c0derMo/DIY-HOTAS/Joystick/STLs/Custom Replacements/Button Holders/Secondary_Trigger_Buttonholder [c0].stl

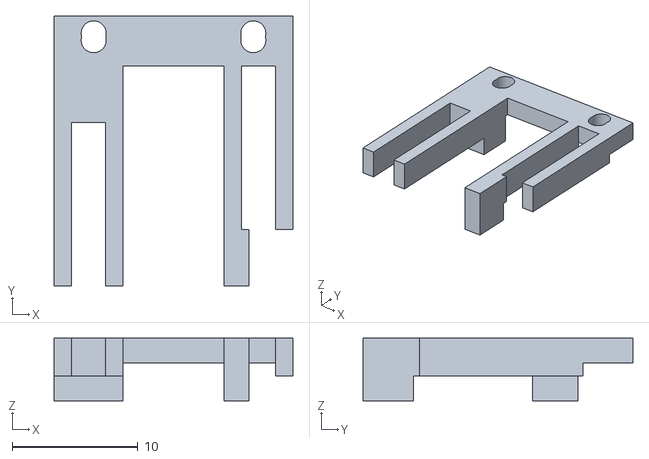
[picture p15: CAD file, 2026-03-30]
Joystick/STLs/Custom Replacements/Button Holders/Secondary_Trigger_Buttonholder [c0].stl
19.0 x 21.5 x 5.00
