c0derMo/DIY-HOTAS/Joystick/STLs/Custom Replacements/Case_Back_With_Mounting_Holes [c0].stl

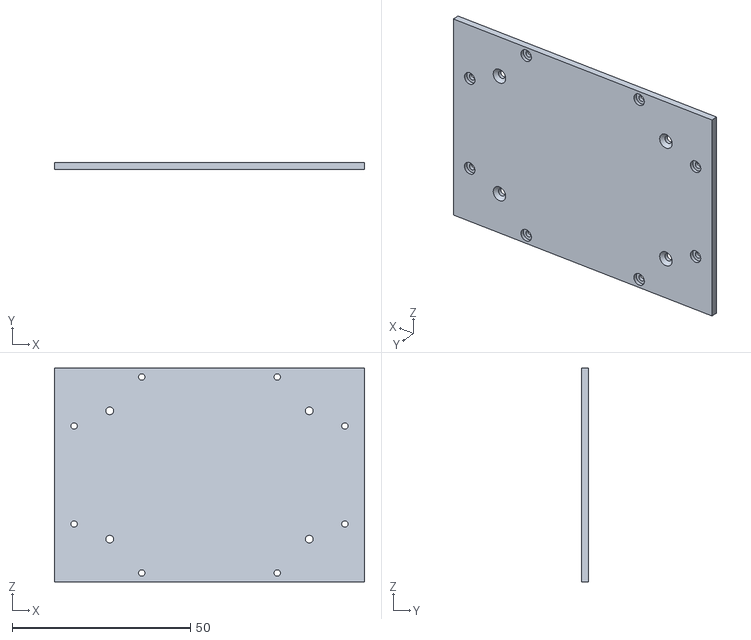
[picture p16: CAD file, 2026-03-30]
Joystick/STLs/Custom Replacements/Case_Back_With_Mounting_Holes [c0].stl
87.0 x 2.00 x 60.0
