c0derMo/DIY-HOTAS/Joystick/STLs/Custom Replacements/Z-Axis/GX12-Bot [c0].stl

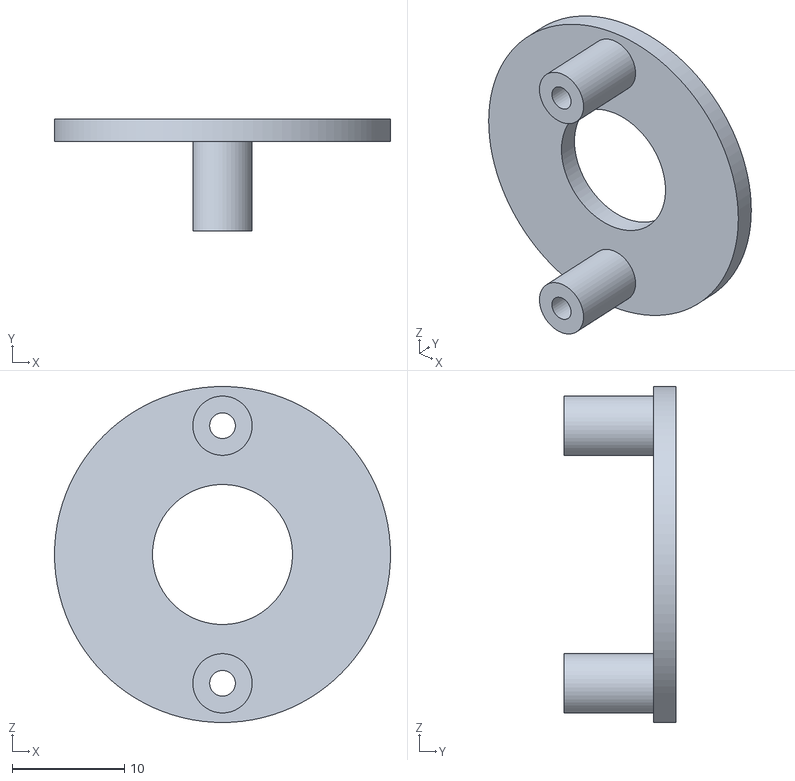
[picture p17: CAD file, 2026-03-30]
Joystick/STLs/Custom Replacements/Z-Axis/GX12-Bot [c0].stl
30.0 x 10.0 x 30.0
