c0derMo/DIY-HOTAS/Joystick/STLs/Gimbal/Gimbal Shaft [B21] [ADD].stl

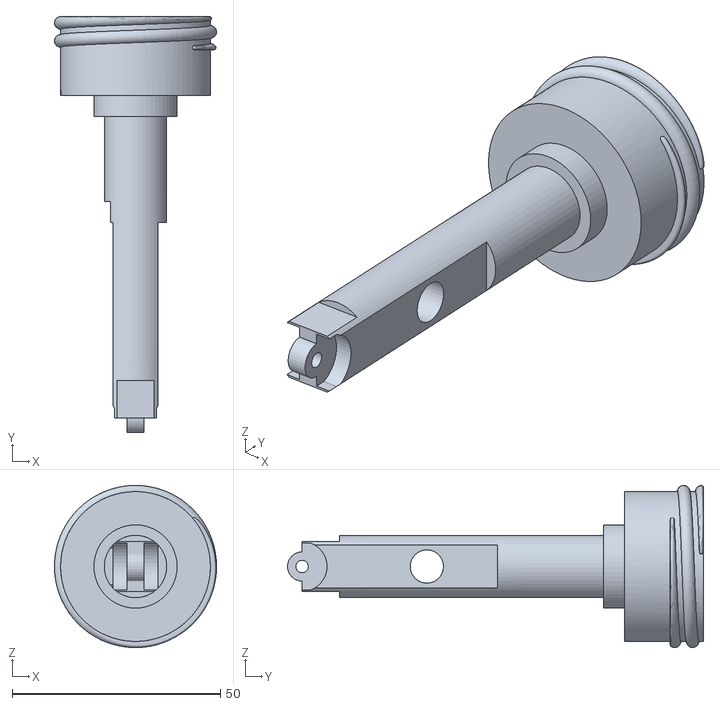
[picture p18: CAD file, 2026-03-30]
Joystick/STLs/Gimbal/Gimbal Shaft [B21] [ADD].stl
39.0 x 100.0 x 39.0
