c0derMo/DIY-HOTAS/Joystick/STLs/Gimbal/GimbalCase/Case Right [B21] [ADD].stl

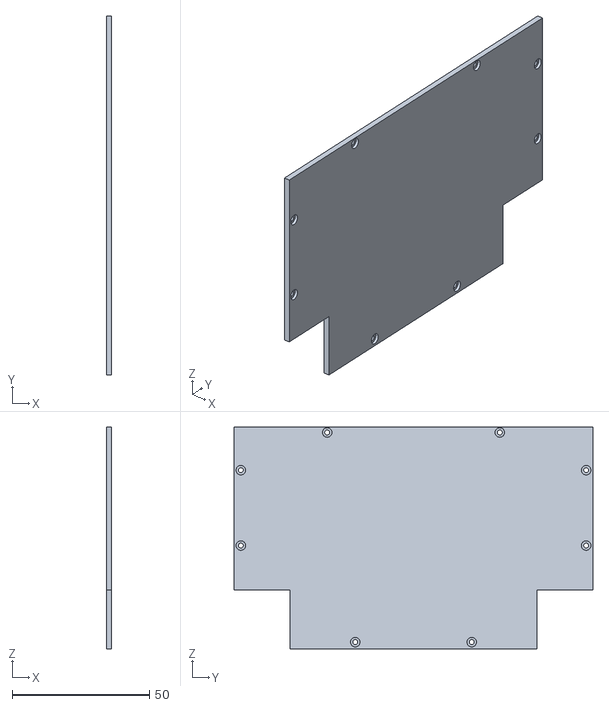
[picture p19: CAD file, 2026-03-30]
Joystick/STLs/Gimbal/GimbalCase/Case Right [B21] [ADD].stl
2.00 x 131.0 x 81.0
