c0derMo/DIY-HOTAS/Joystick/STLs/Head/JoyStick Housing Back [B21].stl

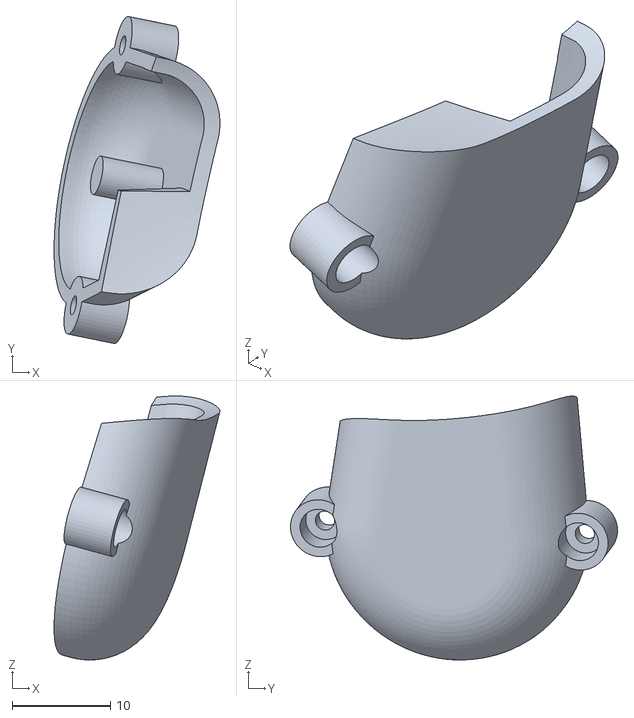
[picture p20: CAD file, 2026-03-30]
Joystick/STLs/Head/JoyStick Housing Back [B21].stl
16.9 x 33.3 x 26.9
