c0derMo/DIY-HOTAS/Joystick/STLs/Head/Tops/Diffuser Top [B21].stl

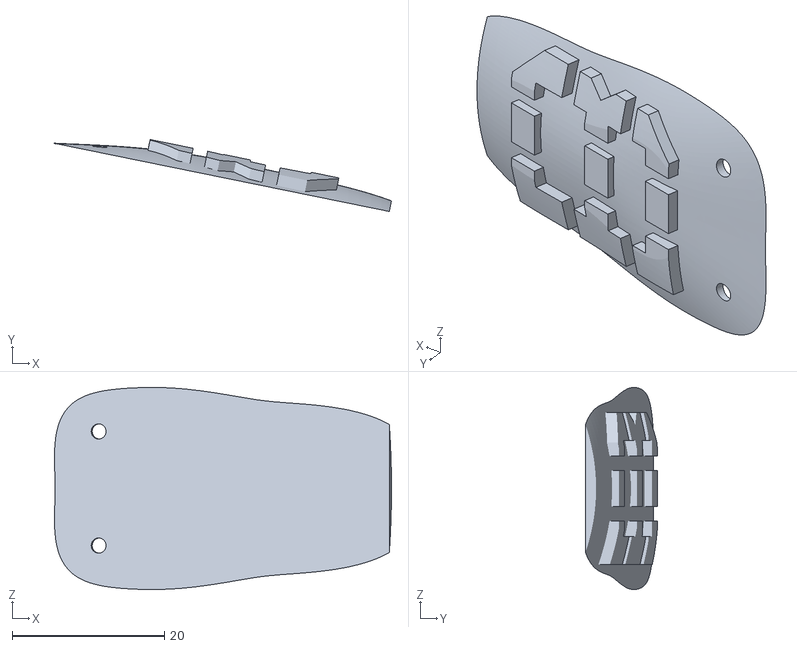
[picture p21: CAD file, 2026-03-30]
Joystick/STLs/Head/Tops/Diffuser Top [B21].stl
44.3 x 9.46 x 26.6
