c0derMo/DIY-HOTAS/Joystick/STLs/Miramaksimus Base Updates/gimbal_frame_as5600.stl

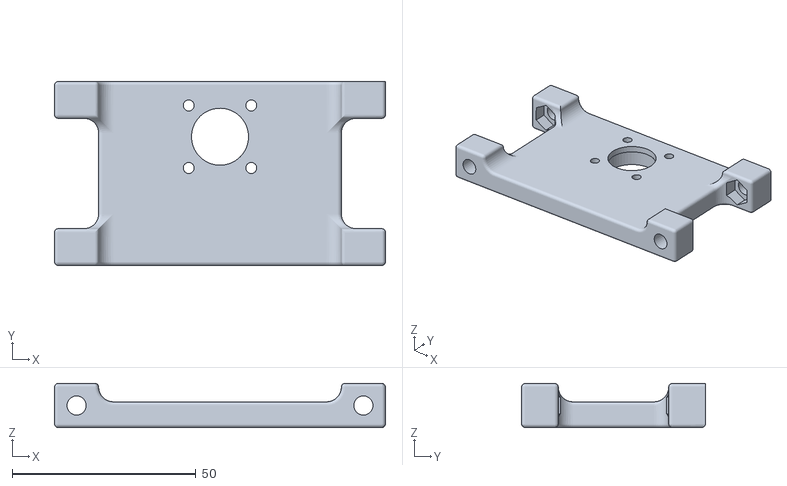
[picture p22: CAD file, 2026-04-03]
Joystick/STLs/Miramaksimus Base Updates/gimbal_frame_as5600.stl
90.0 x 50.0 x 12.0
