c0derMo/DIY-HOTAS/Joystick/STLs/Body/PinkyButton [B21] [ADD].stl

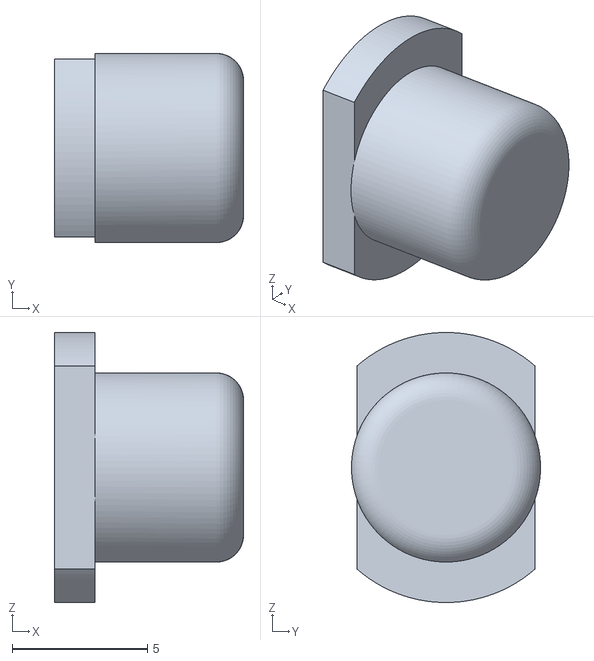
[picture p23: CAD file, 2026-03-30]
Joystick/STLs/Body/PinkyButton [B21] [ADD].stl
7.00 x 7.00 x 10.00
