c0derMo/DIY-HOTAS/Joystick/STLs/Buttons/HS Top 2 [B21].stl

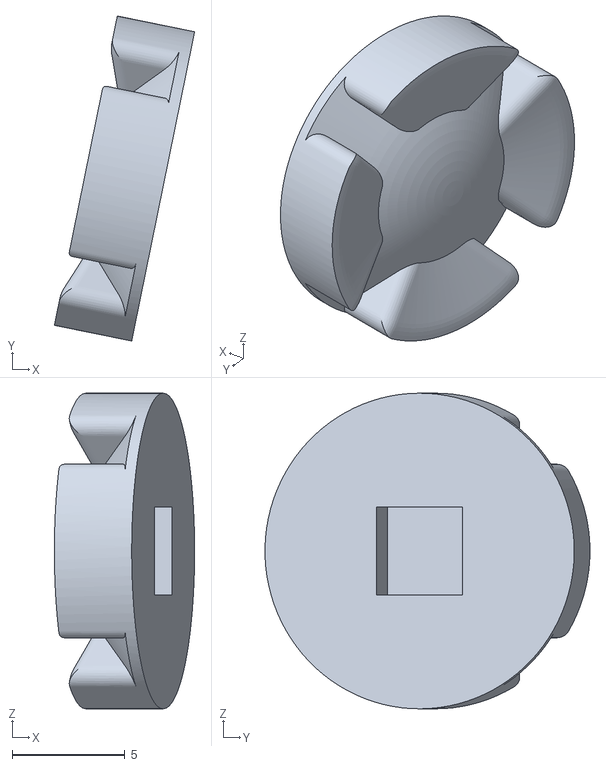
[picture p24: CAD file, 2026-03-30]
Joystick/STLs/Buttons/HS Top 2 [B21].stl
6.22 x 14.4 x 14.0
