c0derMo/DIY-HOTAS/Joystick/STLs/Custom Replacements/Brakelever_Solid [c0].stl

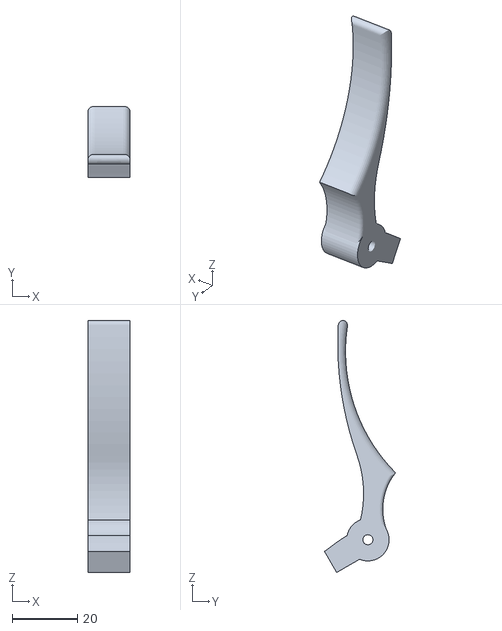
[picture p25: CAD file, 2026-03-30]
Joystick/STLs/Custom Replacements/Brakelever_Solid [c0].stl
13.0 x 21.8 x 77.2
