c0derMo/DIY-HOTAS/Joystick/STLs/Custom Replacements/Button Holders/HAT Thumb Holder [c0].stl

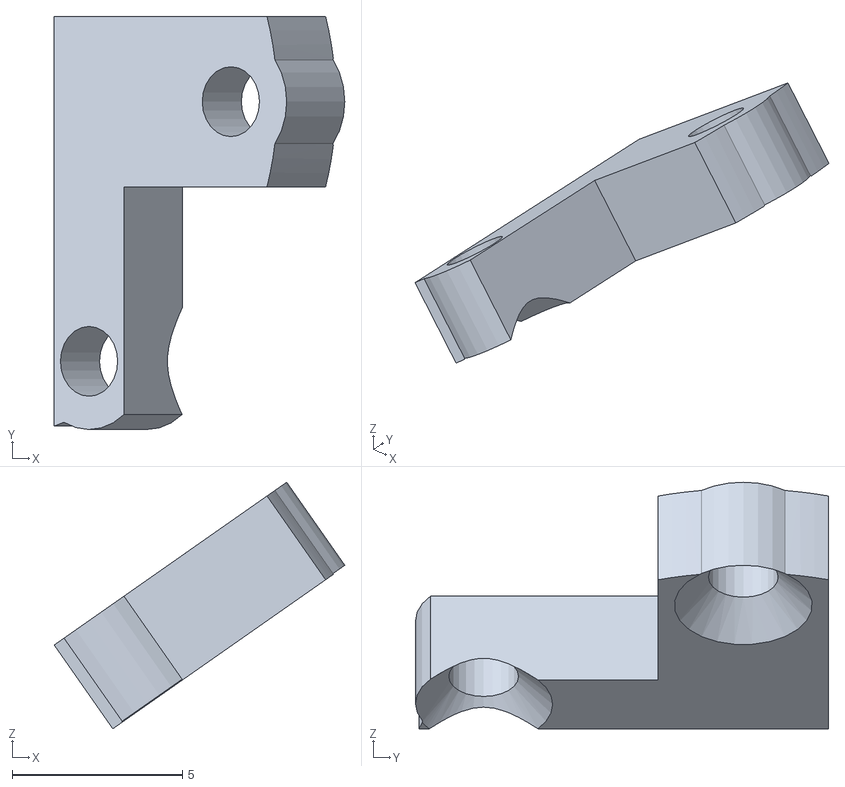
[picture p26: CAD file, 2026-03-30]
Joystick/STLs/Custom Replacements/Button Holders/HAT Thumb Holder [c0].stl
8.53 x 12.1 x 7.24
