c0derMo/DIY-HOTAS/Joystick/STLs/Custom Replacements/Buttons/Button 1 [c0].stl

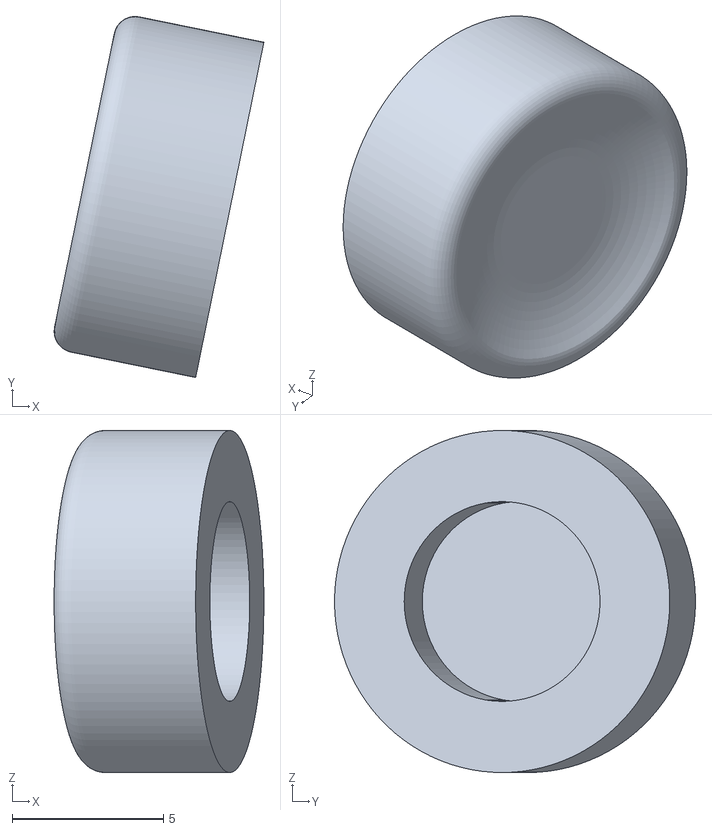
[picture p27: CAD file, 2026-03-30]
Joystick/STLs/Custom Replacements/Buttons/Button 1 [c0].stl
6.93 x 11.9 x 11.3
