c0derMo/DIY-HOTAS/Joystick/STLs/Custom Replacements/Z-Axis/GX12-Top [c0].stl

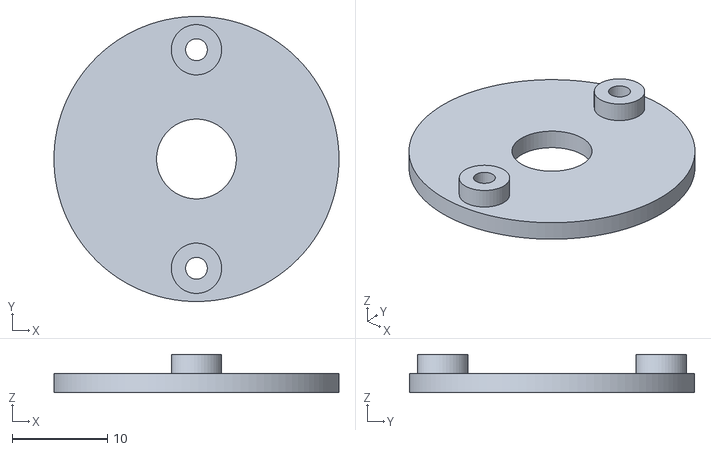
[picture p28: CAD file, 2026-03-30]
Joystick/STLs/Custom Replacements/Z-Axis/GX12-Top [c0].stl
30.0 x 30.0 x 4.00
