c0derMo/DIY-HOTAS/Joystick/STLs/Gimbal/Yaxis Arm V2 [B21] [ADD].stl

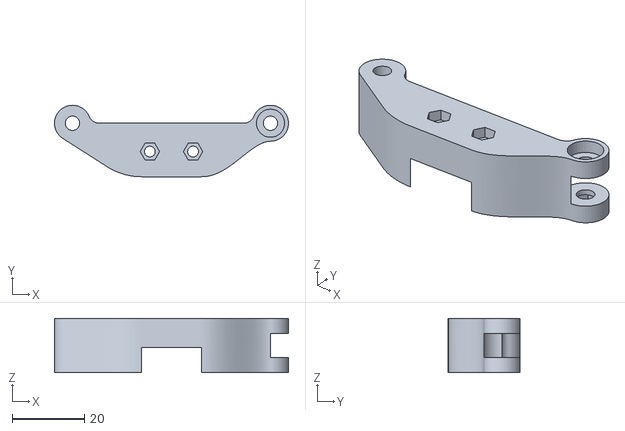
[picture p29: CAD file, 2026-03-30]
Joystick/STLs/Gimbal/Yaxis Arm V2 [B21] [ADD].stl
65.0 x 19.9 x 15.0
