c0derMo/DIY-HOTAS/Joystick/STLs/Head/PCB holder [B21].stl

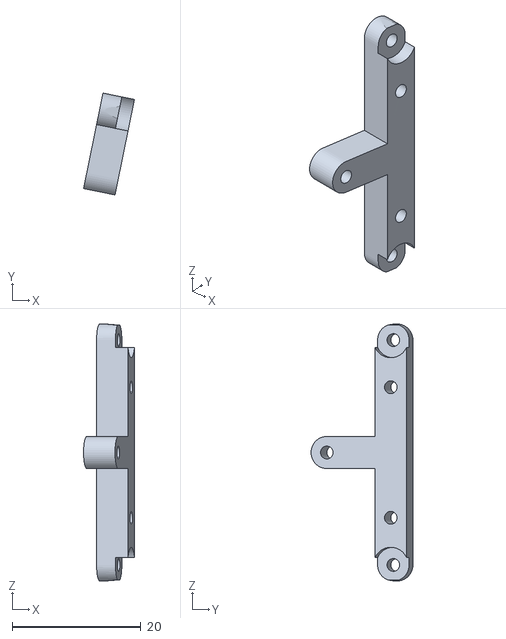
[picture p30: CAD file, 2026-03-30]
Joystick/STLs/Head/PCB holder [B21].stl
7.92 x 15.9 x 40.0
