c0derMo/DIY-HOTAS/Joystick/STLs/Head/Tops/Top Short [B21].stl

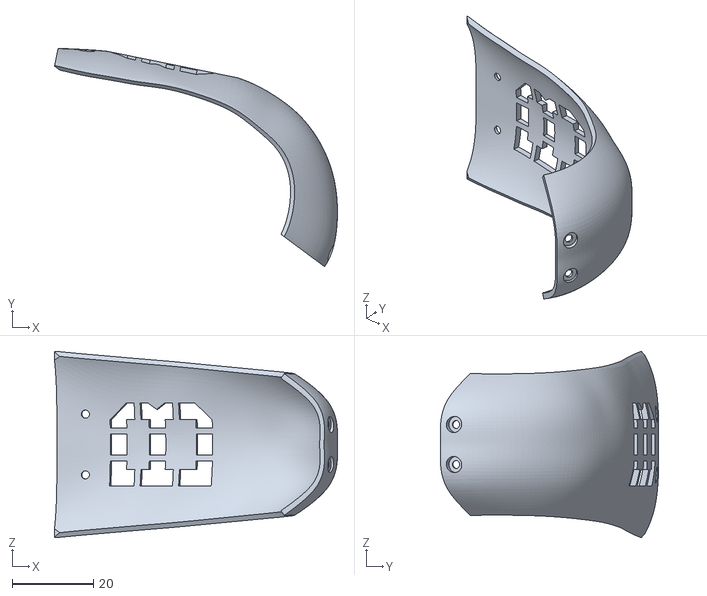
[picture p31: CAD file, 2026-03-30]
Joystick/STLs/Head/Tops/Top Short [B21].stl
69.9 x 53.9 x 46.0
