c0derMo/DIY-HOTAS/Joystick/STLs/Miramaksimus Base Updates/box_frame.stl

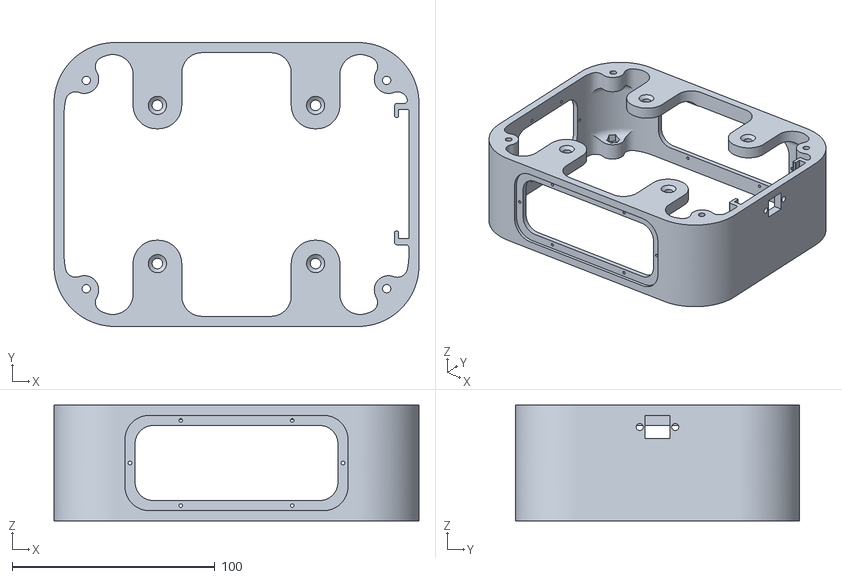
[picture p32: CAD file, 2026-03-30]
Joystick/STLs/Miramaksimus Base Updates/box_frame.stl
180.0 x 140.0 x 57.0
