c0derMo/DIY-HOTAS/Joystick/STLs/ZAxis/Zaxis Connector Top.stl

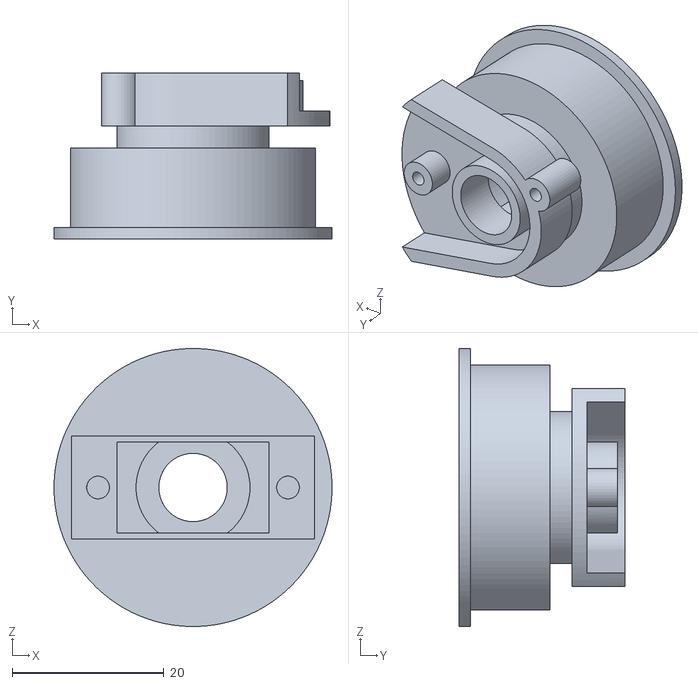
[picture p33: CAD file, 2026-03-30]
Joystick/STLs/ZAxis/Zaxis Connector Top.stl
36.6 x 21.9 x 36.6
