c0derMo/DIY-HOTAS/Joystick/STLs/Body/RighSide R New [B21] [ADD].stl

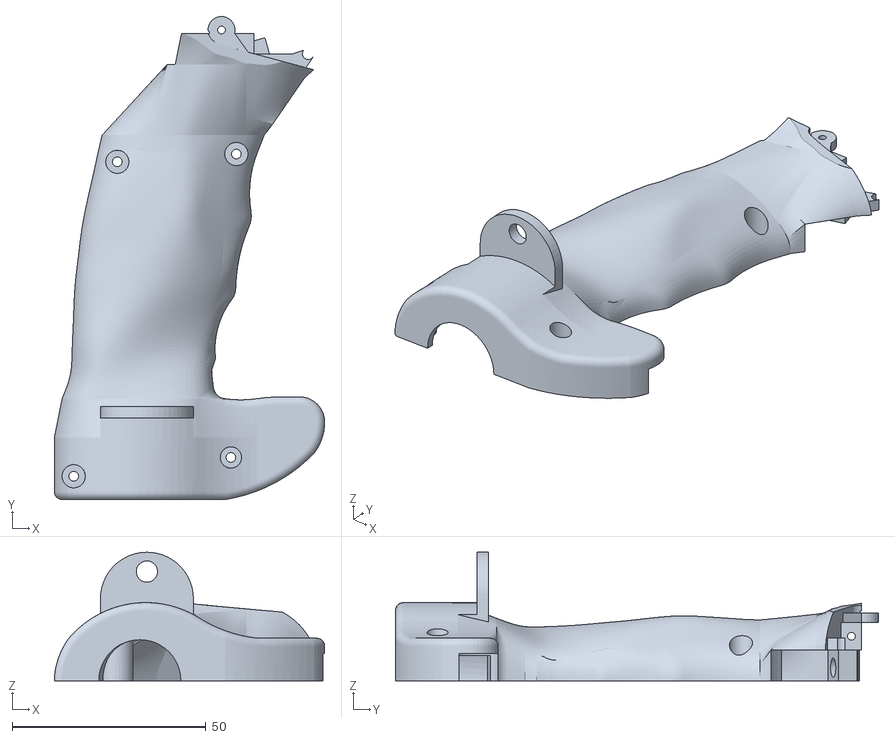
[picture p34: CAD file, 2026-03-30]
Joystick/STLs/Body/RighSide R New [B21] [ADD].stl
69.8 x 124.6 x 33.2
