c0derMo/DIY-HOTAS/Joystick/STLs/Buttons/HS Top [B21].stl

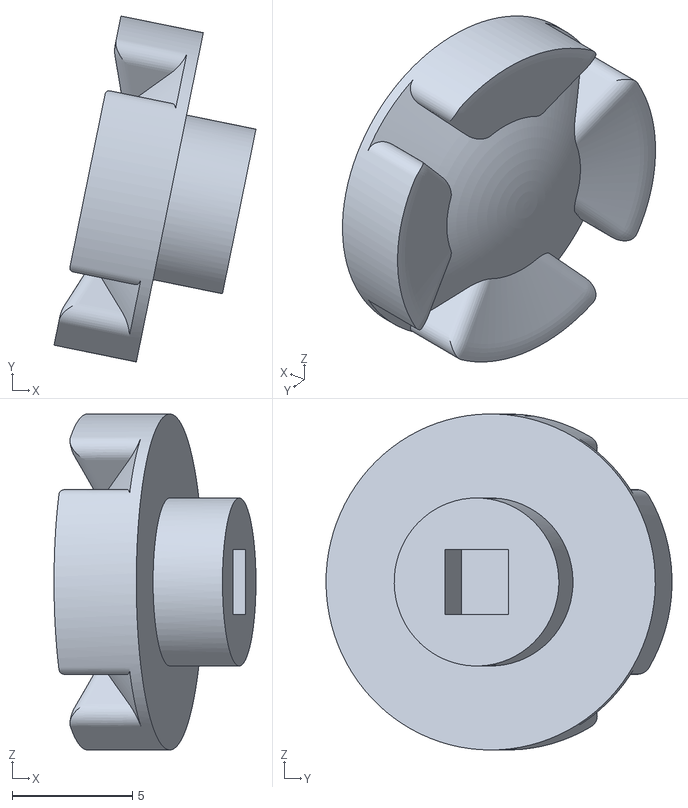
[picture p35: CAD file, 2026-03-30]
Joystick/STLs/Buttons/HS Top [B21].stl
8.41 x 14.4 x 14.0
