c0derMo/DIY-HOTAS/Joystick/STLs/Custom Replacements/Button Holders/frontpanel_holder_bracket [c0].stl

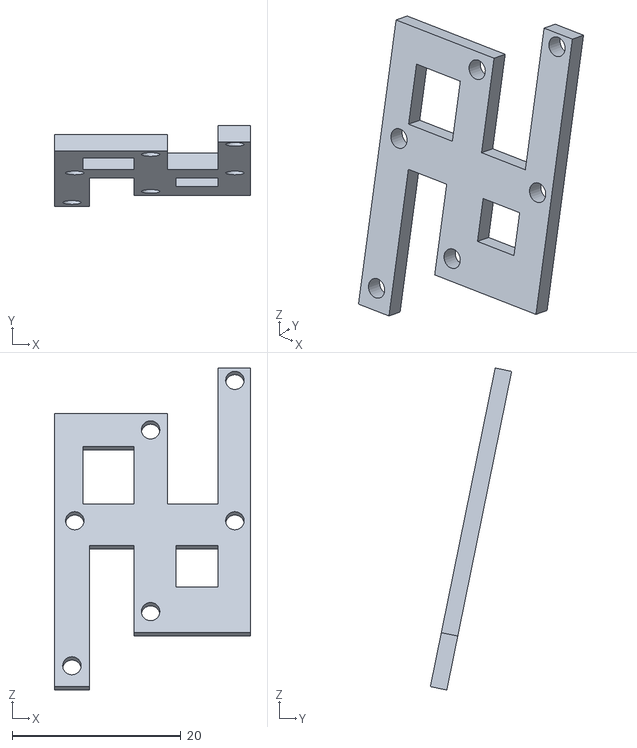
[picture p36: CAD file, 2026-03-30]
Joystick/STLs/Custom Replacements/Button Holders/frontpanel_holder_bracket [c0].stl
23.3 x 9.65 x 38.2
