c0derMo/DIY-HOTAS/Joystick/STLs/Custom Replacements/Buttons/HS Top [c0].stl

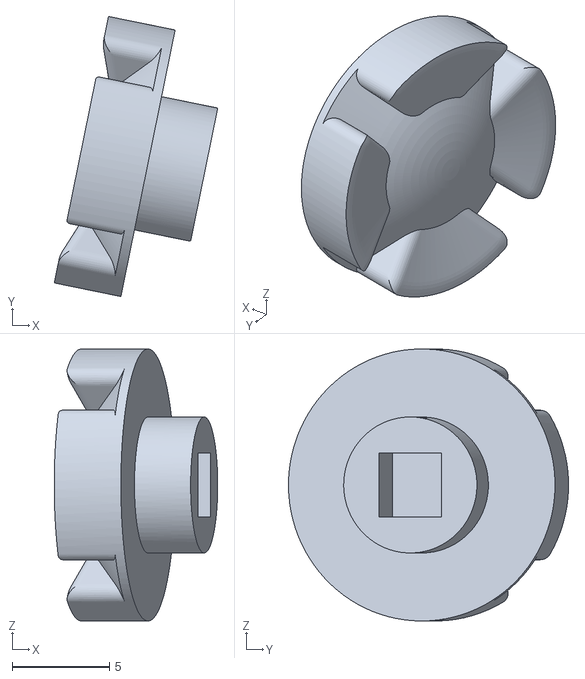
[picture p37: CAD file, 2026-03-30]
Joystick/STLs/Custom Replacements/Buttons/HS Top [c0].stl
8.41 x 14.4 x 14.0
