c0derMo/DIY-HOTAS/Joystick/STLs/Custom Replacements/Z-Axis/Axis-Top-Connectorindependent-no-zaxis [c0].stl

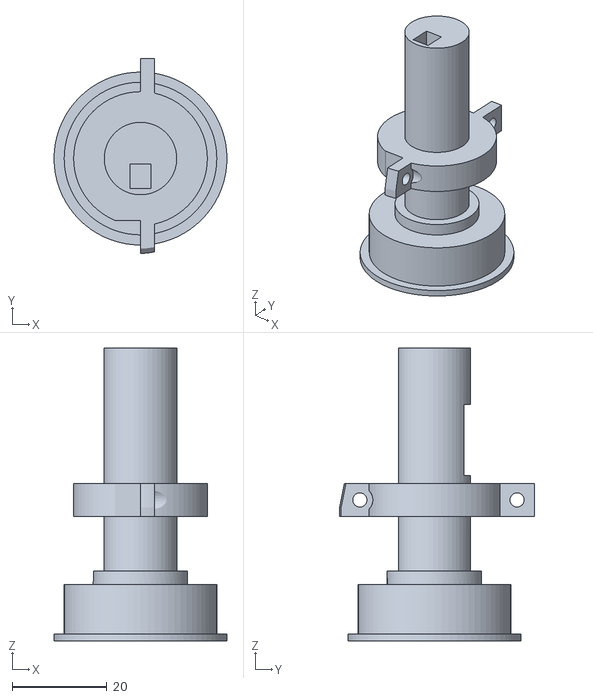
[picture p38: CAD file, 2026-03-30]
Joystick/STLs/Custom Replacements/Z-Axis/Axis-Top-Connectorindependent-no-zaxis [c0].stl
36.6 x 41.2 x 62.0
