c0derMo/DIY-HOTAS/Joystick/STLs/Gimbal/Y Cam V2 [B21] [ADD].stl

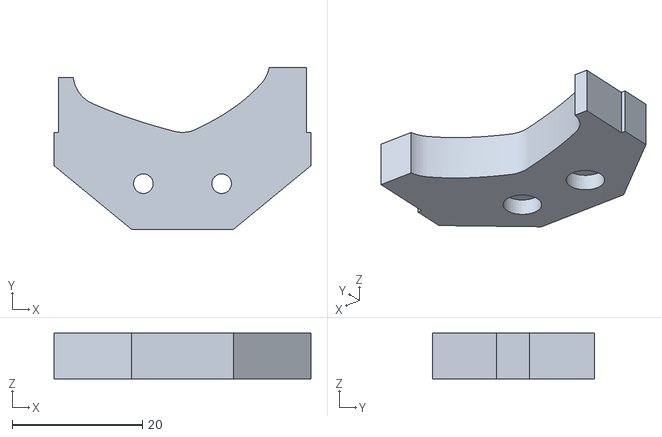
[picture p39: CAD file, 2026-03-30]
Joystick/STLs/Gimbal/Y Cam V2 [B21] [ADD].stl
39.4 x 24.8 x 7.00
