c0derMo/DIY-HOTAS/Joystick/STLs/Head/Head Body [B21] [ADD].stl

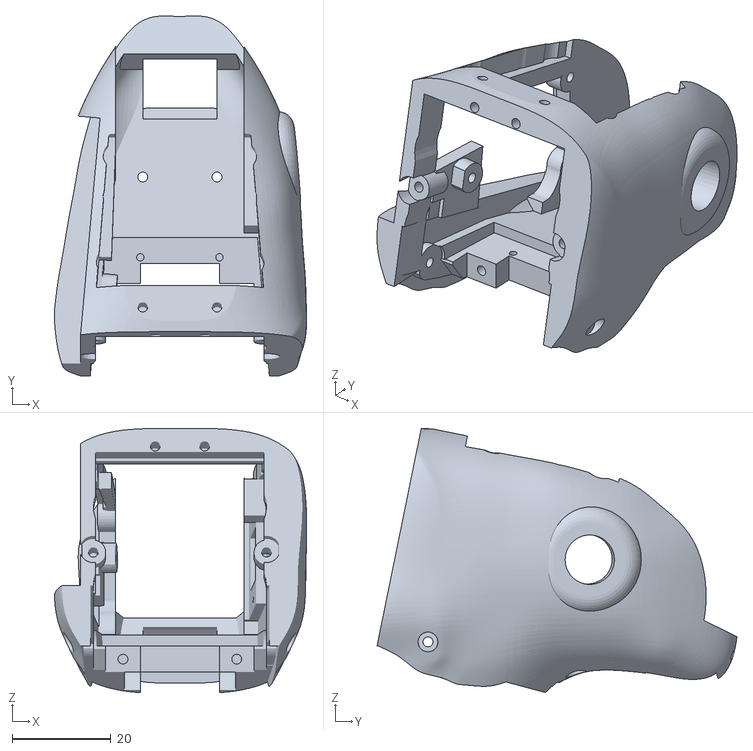
[picture p40: CAD file, 2026-03-30]
Joystick/STLs/Head/Head Body [B21] [ADD].stl
51.0 x 72.8 x 53.4
