c0derMo/DIY-HOTAS/Joystick/STLs/Miramaksimus Base Updates/gimbal_core_non_pot_side.stl

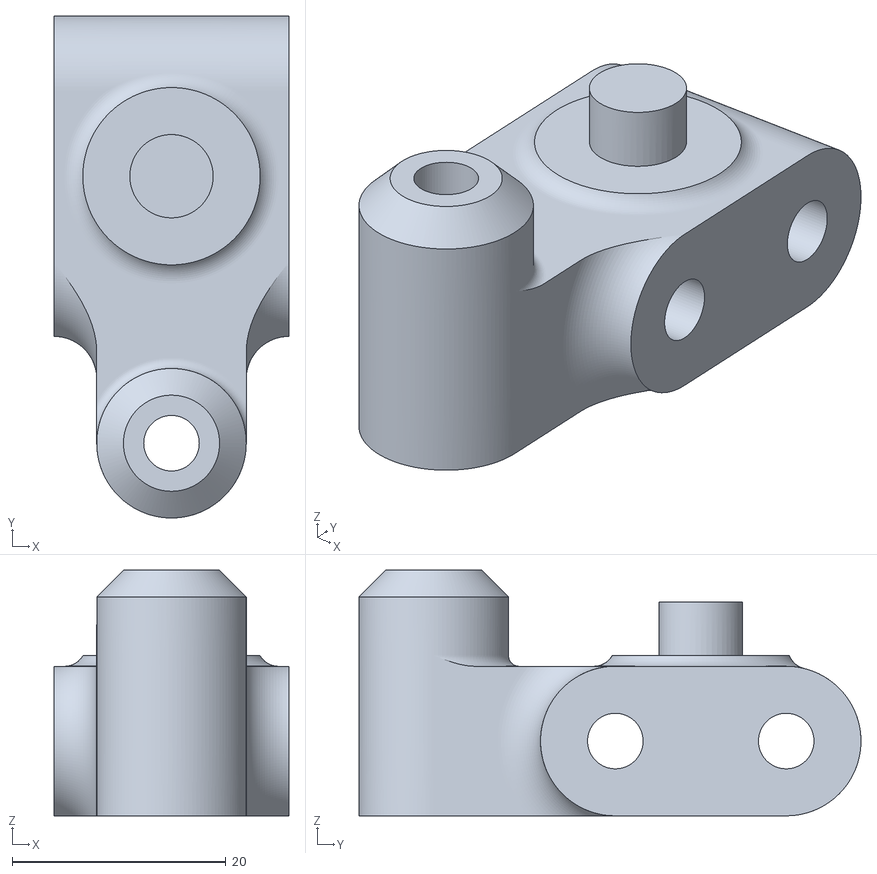
[picture p41: CAD file, 2026-03-30]
Joystick/STLs/Miramaksimus Base Updates/gimbal_core_non_pot_side.stl
22.0 x 47.0 x 23.0
