c0derMo/DIY-HOTAS/Joystick/STLs/ZAxis/Bearing HallEffect.stl

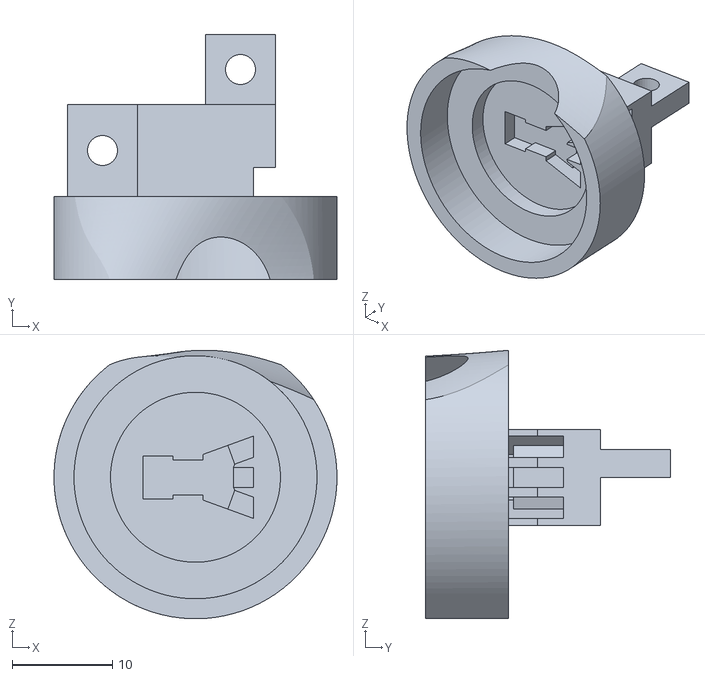
[picture p42: CAD file, 2026-03-30]
Joystick/STLs/ZAxis/Bearing HallEffect.stl
28.3 x 24.5 x 26.8
