c0derMo/DIY-HOTAS/Joystick/STLs/Buttons/Joy Stick Cap [B21].stl

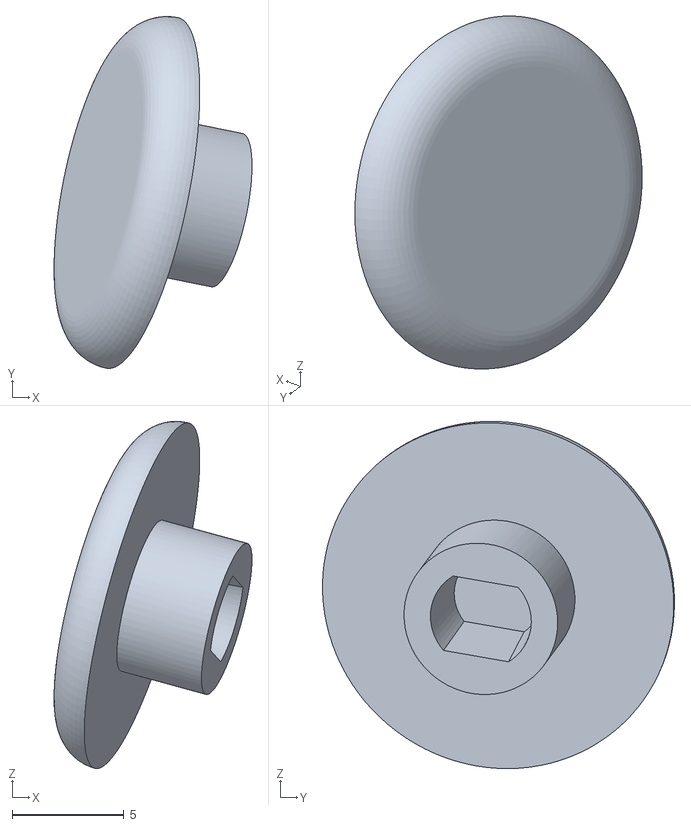
[picture p43: CAD file, 2026-03-30]
Joystick/STLs/Buttons/Joy Stick Cap [B21].stl
8.85 x 15.7 x 15.5
