c0derMo/DIY-HOTAS/Joystick/STLs/Custom Replacements/Button Holders/Frontpanel_Holder [c0].stl

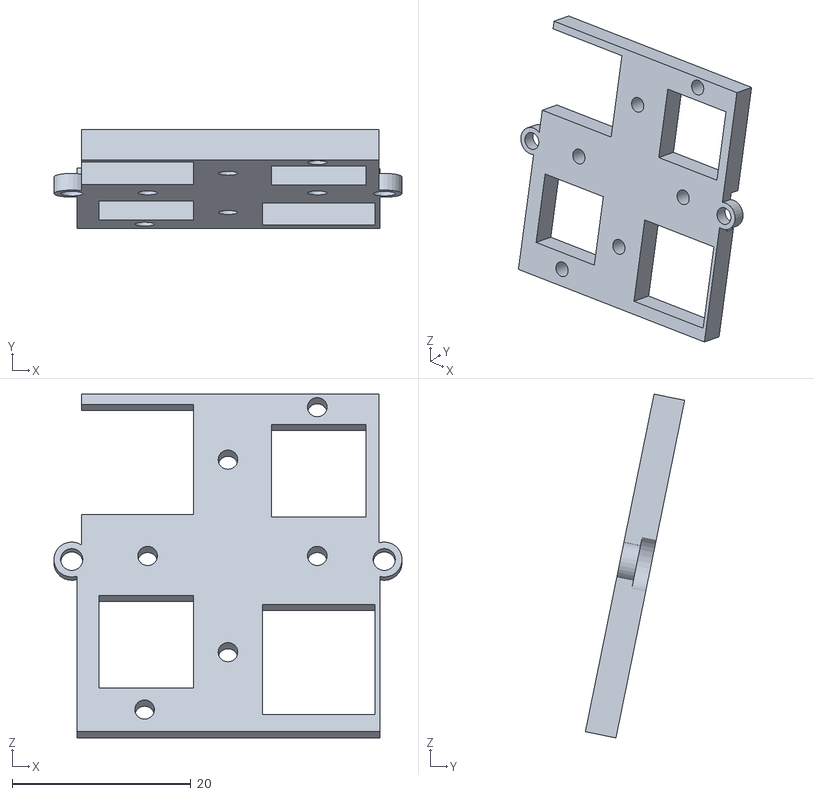
[picture p44: CAD file, 2026-03-30]
Joystick/STLs/Custom Replacements/Button Holders/Frontpanel_Holder [c0].stl
39.0 x 11.1 x 38.5
