c0derMo/DIY-HOTAS/Joystick/STLs/Gimbal/Xaxis Cariage V2 [B21] [ADD].stl

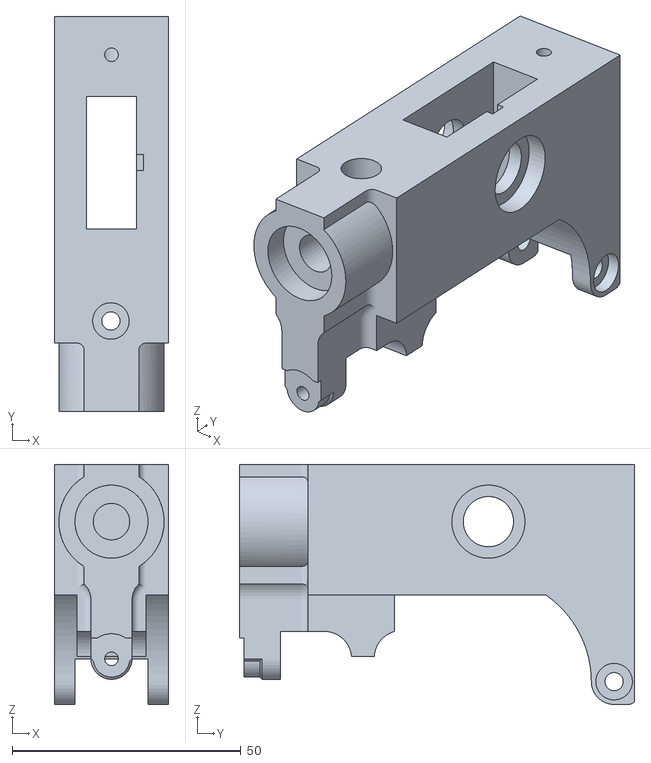
[picture p45: CAD file, 2026-03-30]
Joystick/STLs/Gimbal/Xaxis Cariage V2 [B21] [ADD].stl
25.0 x 86.5 x 52.5
