c0derMo/DIY-HOTAS/Joystick/STLs/Head/Secondary Trigger SpringLever.stl

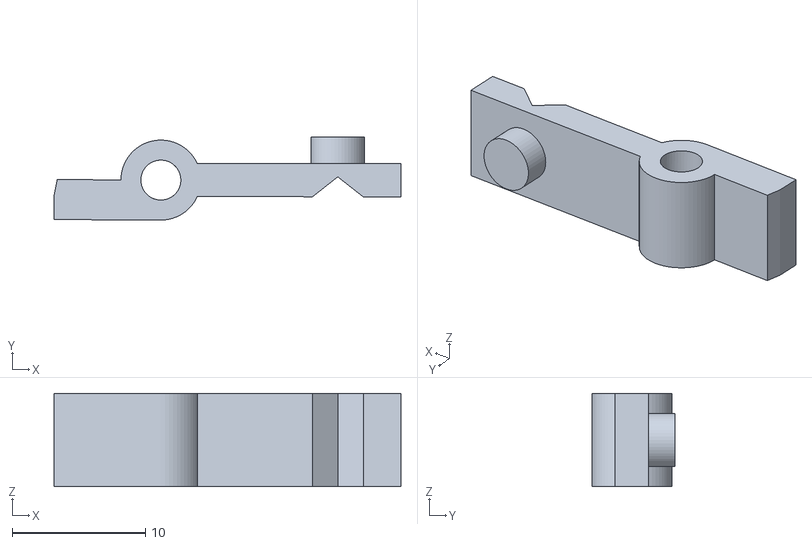
[picture p46: CAD file, 2026-03-30]
Joystick/STLs/Head/Secondary Trigger SpringLever.stl
26.0 x 6.24 x 7.00
