c0derMo/DIY-HOTAS/Joystick/STLs/Head/Tops/Top Extended [B21].stl

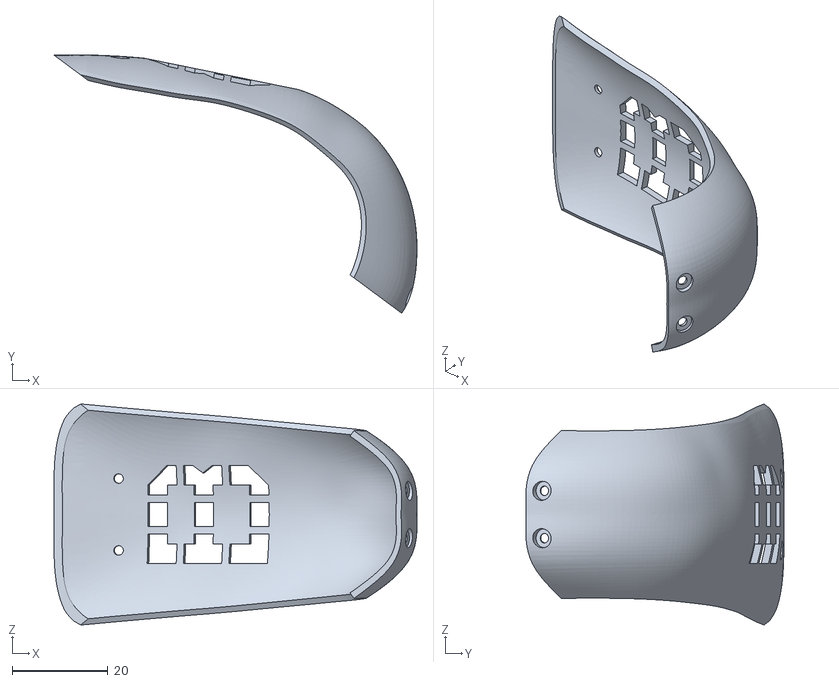
[picture p47: CAD file, 2026-03-30]
Joystick/STLs/Head/Tops/Top Extended [B21].stl
75.7 x 53.9 x 46.1
