c0derMo/DIY-HOTAS/Joystick/STLs/Miramaksimus Base Updates/gimbal_frame.stl

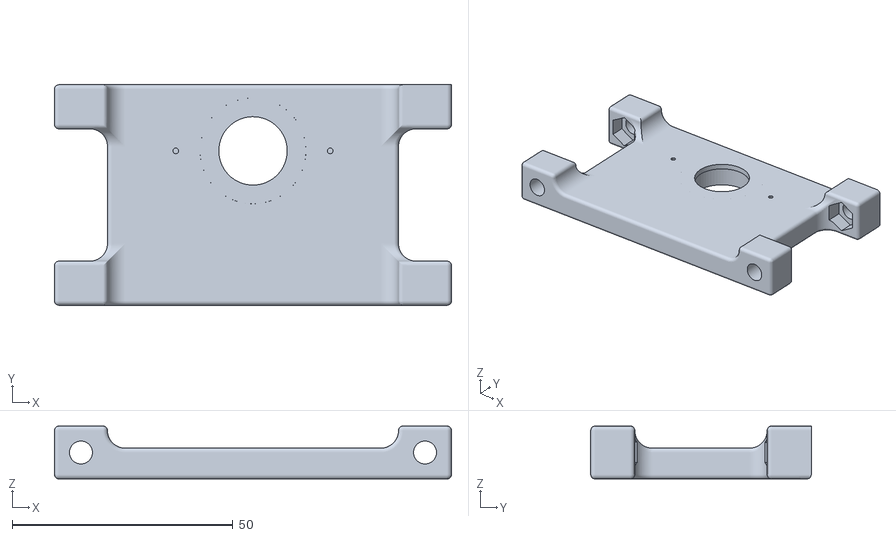
[picture p48: CAD file, 2026-03-30]
Joystick/STLs/Miramaksimus Base Updates/gimbal_frame.stl
90.0 x 50.0 x 12.0
