c0derMo/DIY-HOTAS/Joystick/STLs/ZAxis/BearingHolder.stl

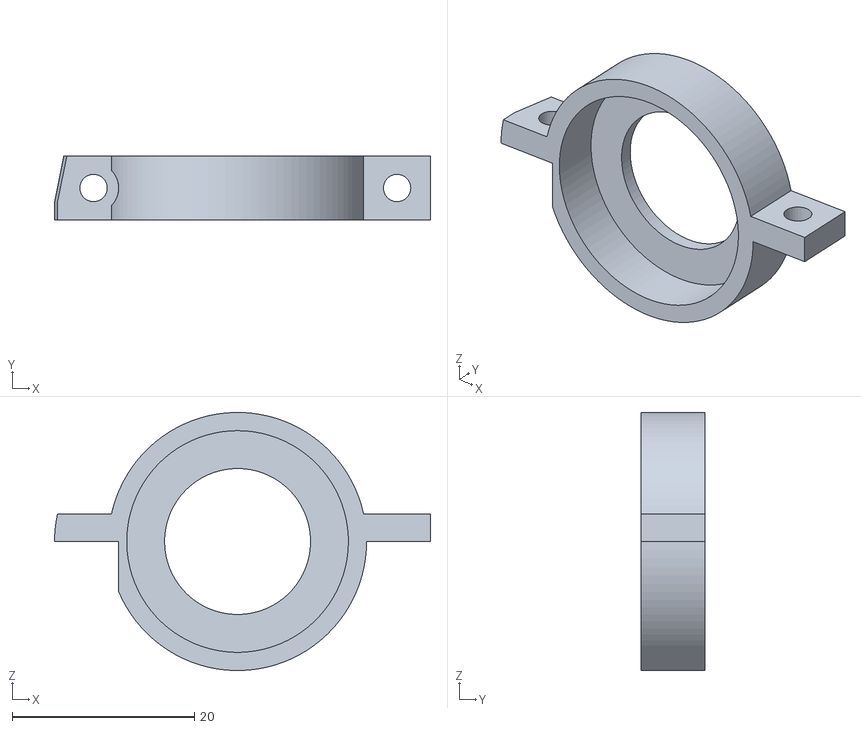
[picture p49: CAD file, 2026-03-30]
Joystick/STLs/ZAxis/BearingHolder.stl
41.2 x 7.00 x 28.3
