c0derMo/DIY-HOTAS/Joystick/STLs/Body/Momentary Trigger [B21 [ADD].stl

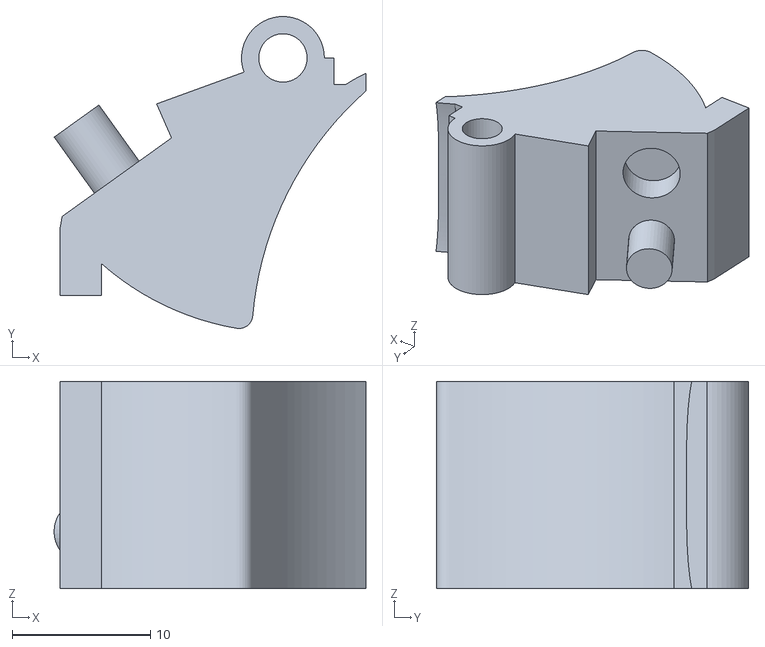
[picture p50: CAD file, 2026-03-30]
Joystick/STLs/Body/Momentary Trigger [B21 [ADD].stl
22.6 x 22.6 x 15.0
