c0derMo/DIY-HOTAS/Joystick/STLs/Buttons/Button 1 [B21].stl

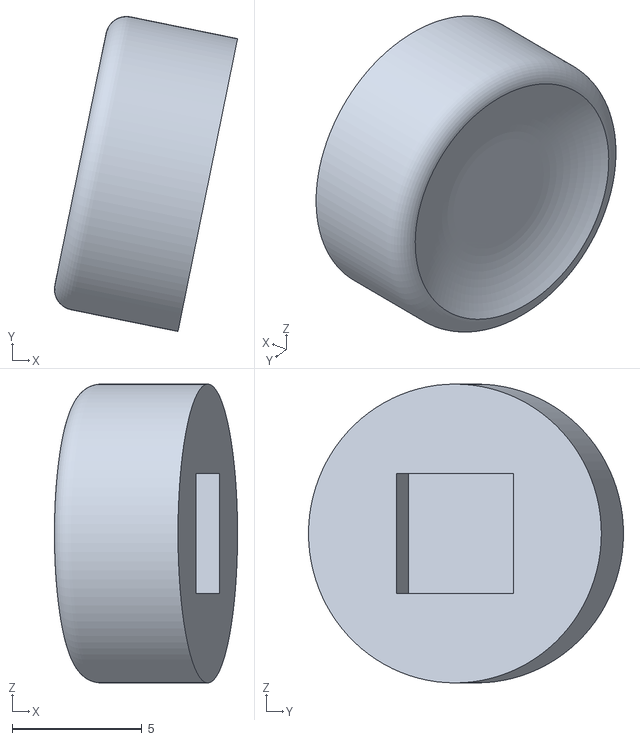
[picture p51: CAD file, 2026-03-30]
Joystick/STLs/Buttons/Button 1 [B21].stl
7.05 x 12.1 x 11.5
