c0derMo/DIY-HOTAS/Joystick/STLs/Gimbal/GimbalCase/Large Ring [B21] [ADD].stl

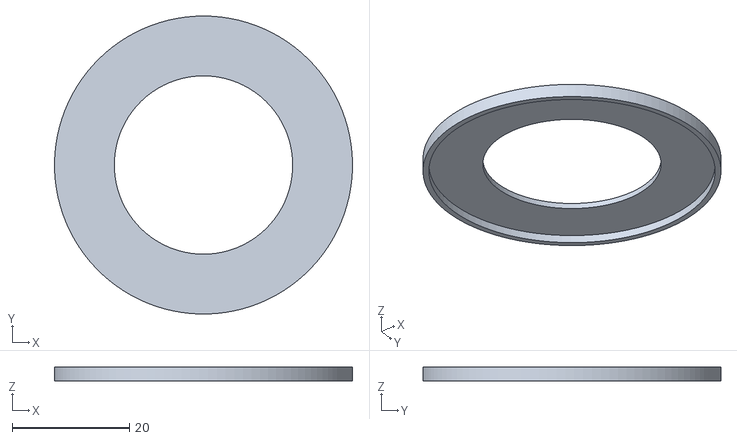
[picture p52: CAD file, 2026-03-30]
Joystick/STLs/Gimbal/GimbalCase/Large Ring [B21] [ADD].stl
50.8 x 50.8 x 2.40
