c0derMo/DIY-HOTAS/Joystick/STLs/Gimbal/XCam1 V3 [B21] [ADD].stl

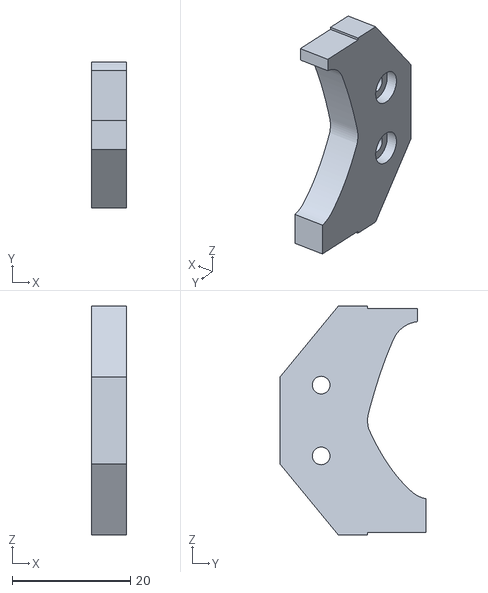
[picture p53: CAD file, 2026-03-30]
Joystick/STLs/Gimbal/XCam1 V3 [B21] [ADD].stl
6.00 x 24.8 x 38.8
