c0derMo/DIY-HOTAS/Joystick/STLs/Head/Front Button JoyStick [B21].stl

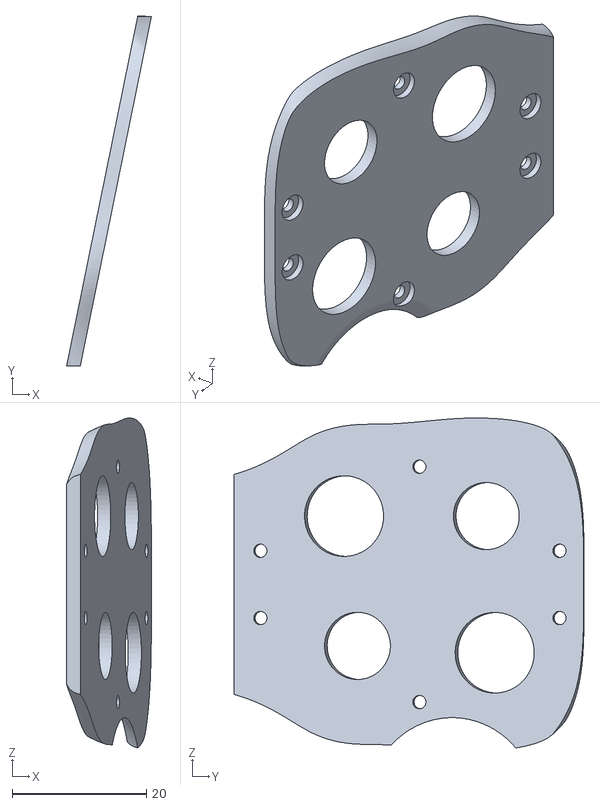
[picture p54: CAD file, 2026-03-30]
Joystick/STLs/Head/Front Button JoyStick [B21].stl
12.6 x 52.0 x 49.1
