c0derMo/DIY-HOTAS/Joystick/STLs/Head/Tops/LEDseparator V2 [B21].stl

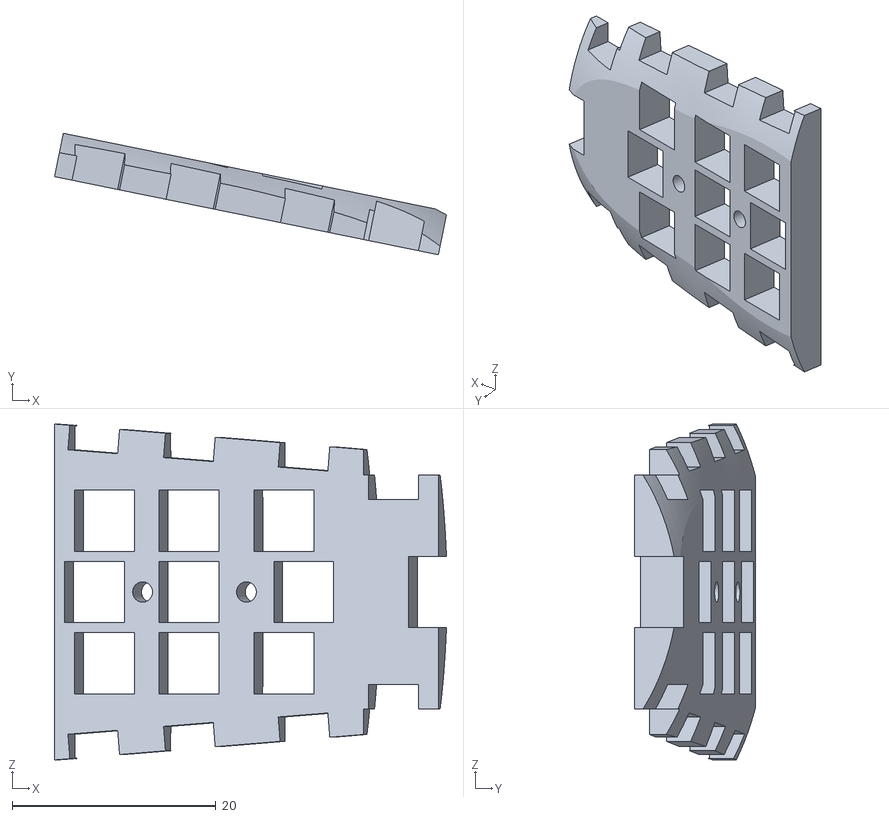
[picture p55: CAD file, 2026-03-30]
Joystick/STLs/Head/Tops/LEDseparator V2 [B21].stl
38.5 x 11.9 x 33.0
