c0derMo/DIY-HOTAS/Joystick/STLs/ZAxis/Zaxis topMag.stl

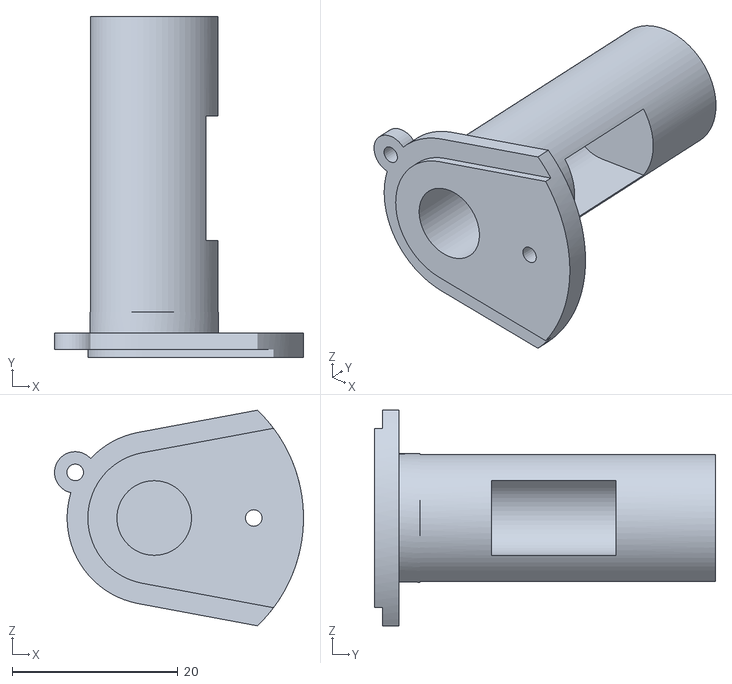
[picture p57: CAD file, 2026-03-30]
Joystick/STLs/ZAxis/Zaxis topMag.stl
30.0 x 41.1 x 26.0
