c0derMo/DIY-HOTAS/Joystick/STLs/Gimbal/GimbalCase/Smol Ring [B21] [ADD].stl

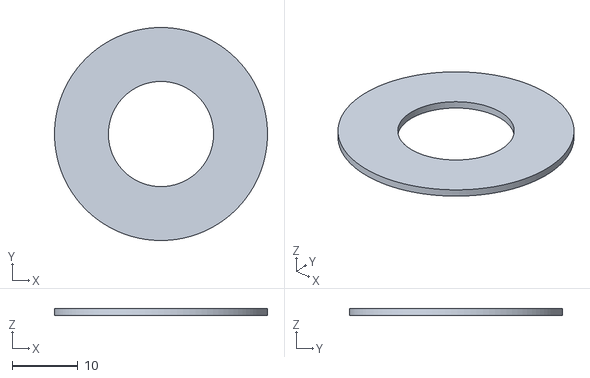
[picture p58: CAD file, 2026-03-30]
Joystick/STLs/Gimbal/GimbalCase/Smol Ring [B21] [ADD].stl
32.4 x 32.4 x 1.00
