c0derMo/DIY-HOTAS/Joystick/STLs/Gimbal/Xaxis Arm V2 [B21] [ADD].stl

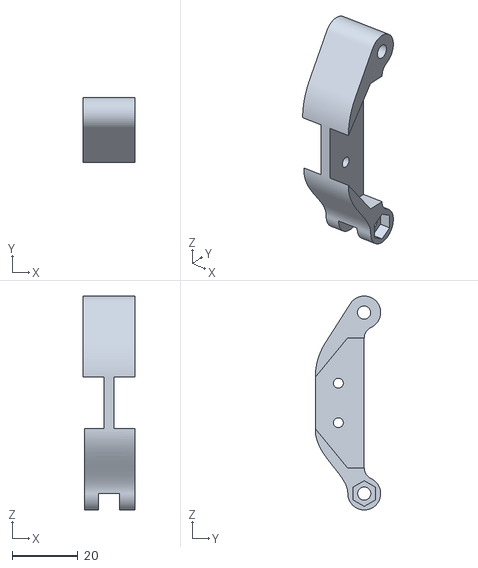
[picture p59: CAD file, 2026-03-30]
Joystick/STLs/Gimbal/Xaxis Arm V2 [B21] [ADD].stl
15.8 x 19.9 x 65.0
