c0derMo/DIY-HOTAS/Joystick/STLs/Head/Left Panel JoyStick [B21] [ADD].stl

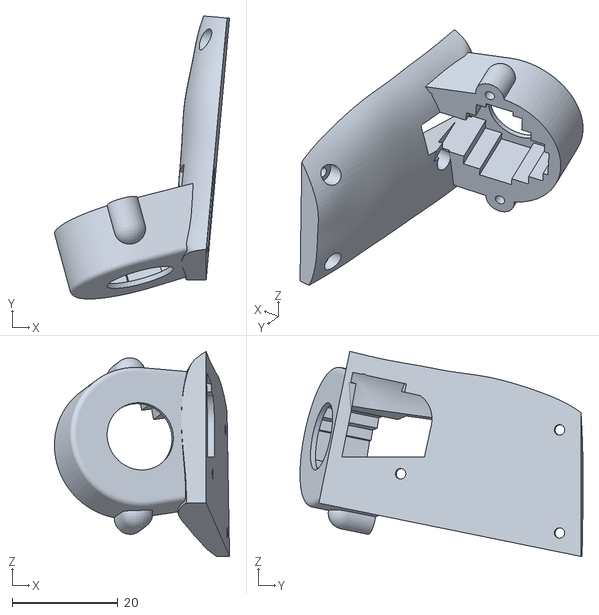
[picture p60: CAD file, 2026-03-30]
Joystick/STLs/Head/Left Panel JoyStick [B21] [ADD].stl
33.2 x 53.6 x 38.9
