c0derMo/DIY-HOTAS/Joystick/STLs/Head/Tops/DiffuserV3 [B21] [ADD].stl

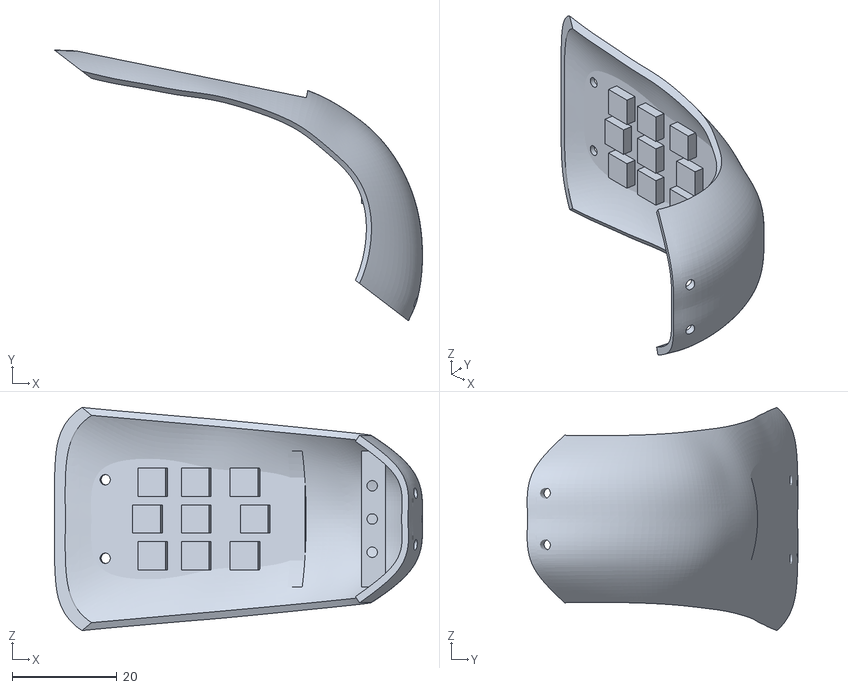
[picture p61: CAD file, 2026-03-30]
Joystick/STLs/Head/Tops/DiffuserV3 [B21] [ADD].stl
70.3 x 51.7 x 42.6
