c0derMo/DIY-HOTAS/Joystick/STLs/Miramaksimus Base Updates/49E Hall Sensor Holder.stl

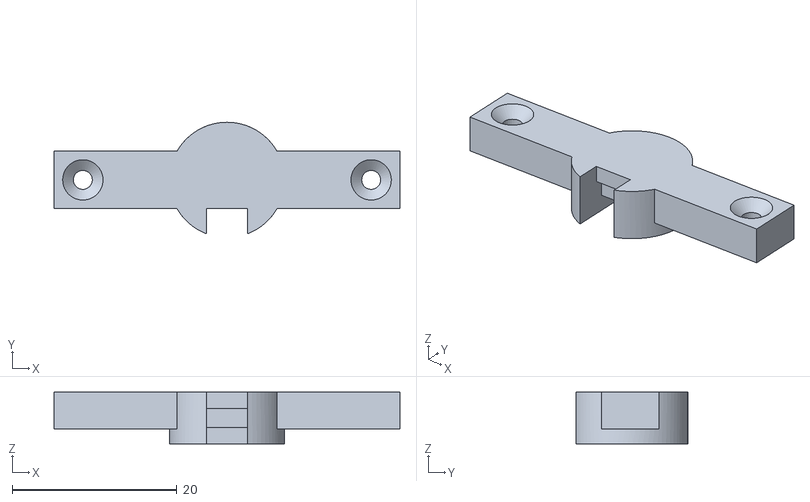
[picture p62: CAD file, 2026-03-30]
Joystick/STLs/Miramaksimus Base Updates/49E Hall Sensor Holder.stl
42.0 x 13.5 x 6.30
