c0derMo/DIY-HOTAS/Joystick/STLs/Buttons/Thumb Hat 2 [ADD].stl

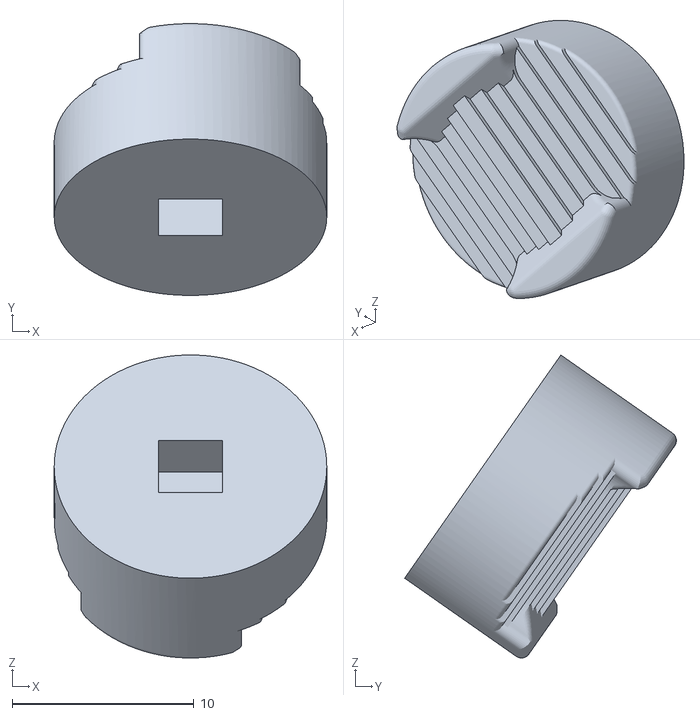
[picture p63: CAD file, 2026-03-30]
Joystick/STLs/Buttons/Thumb Hat 2 [ADD].stl
15.0 x 15.0 x 16.7
