c0derMo/DIY-HOTAS/Joystick/STLs/Gimbal/GimbalCase/Medium ring [B21] [ADD].stl

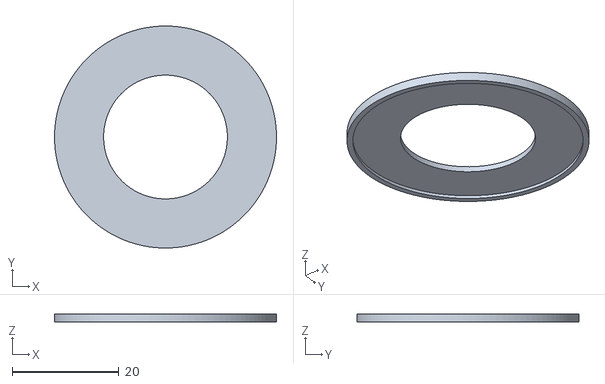
[picture p64: CAD file, 2026-03-30]
Joystick/STLs/Gimbal/GimbalCase/Medium ring [B21] [ADD].stl
41.6 x 41.6 x 1.58
