c0derMo/DIY-HOTAS/Joystick/STLs/Miramaksimus Base Updates/Bearing Adapter.stl

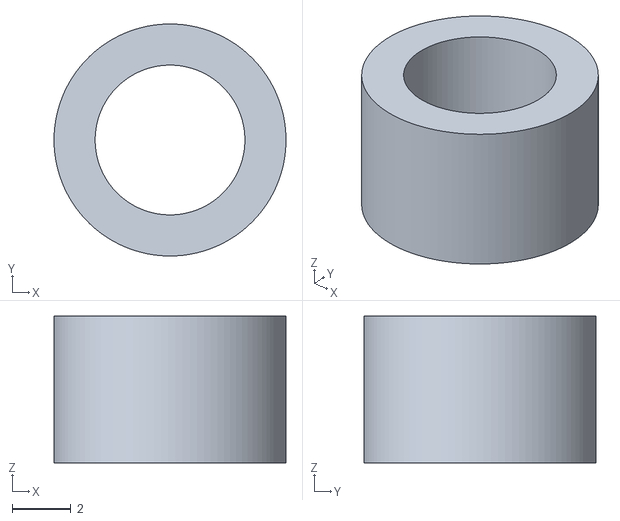
[picture p65: CAD file, 2026-03-30]
Joystick/STLs/Miramaksimus Base Updates/Bearing Adapter.stl
7.90 x 7.90 x 5.00
