c0derMo/DIY-HOTAS/Joystick/STLs/Gimbal/X-Y Connector V2 [B21} [ADD}.stl

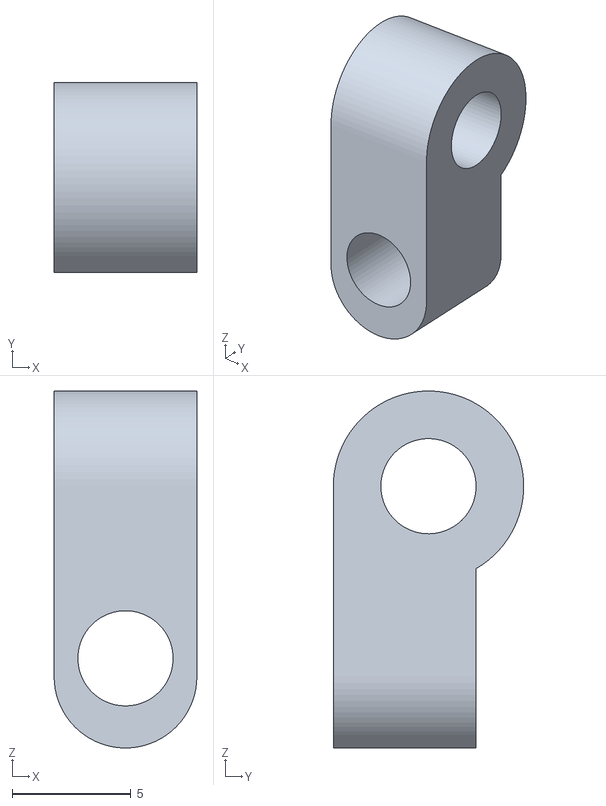
[picture p67: CAD file, 2026-03-30]
Joystick/STLs/Gimbal/X-Y Connector V2 [B21} [ADD}.stl
6.00 x 8.00 x 15.0
