c0derMo/DIY-HOTAS/Joystick/STLs/Miramaksimus Base Updates/gimbal_lever_arm.stl

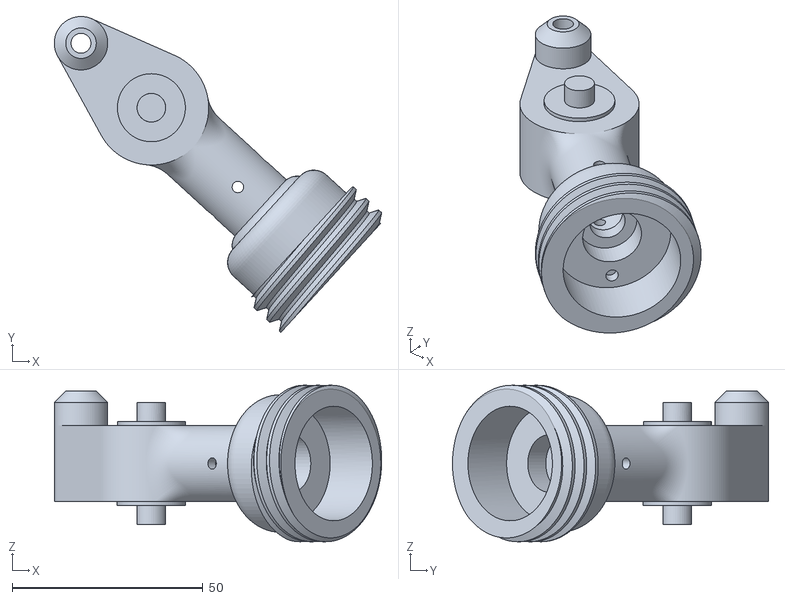
[picture p68: CAD file, 2026-03-30]
Joystick/STLs/Miramaksimus Base Updates/gimbal_lever_arm.stl
85.8 x 82.8 x 41.0
