c0derMo/DIY-HOTAS/Joystick/STLs/Gimbal/GimbalCase/Case Upper [B21] [ADD].stl

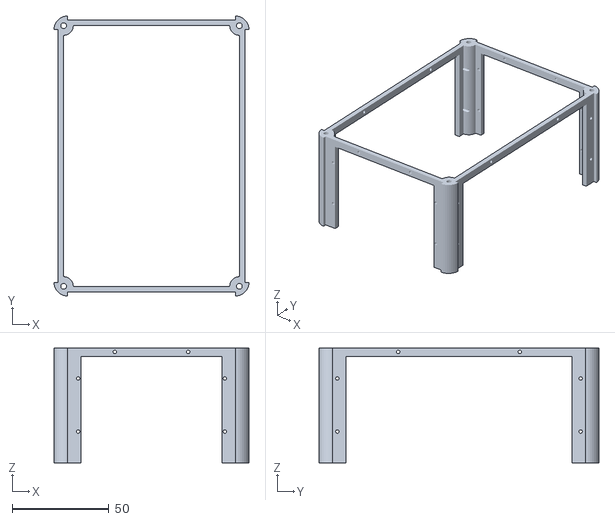
[picture p69: CAD file, 2026-03-30]
Joystick/STLs/Gimbal/GimbalCase/Case Upper [B21] [ADD].stl
101.0 x 145.0 x 59.5
