c0derMo/DIY-HOTAS/Joystick/STLs/Miramaksimus Base Updates/gimbal_core_bearing_carrier_alt.stl

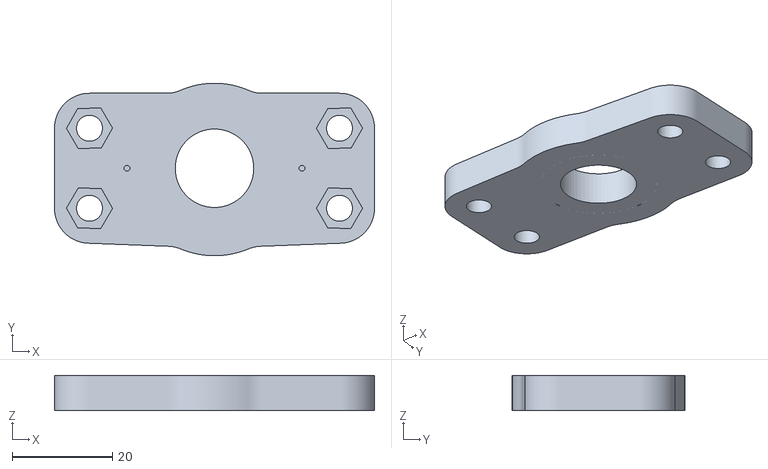
[picture p70: CAD file, 2026-03-30]
Joystick/STLs/Miramaksimus Base Updates/gimbal_core_bearing_carrier_alt.stl
64.0 x 34.5 x 7.00
