c0derMo/DIY-HOTAS/Joystick/STLs/Miramaksimus Base Updates/gimbal_core_pot_side.stl

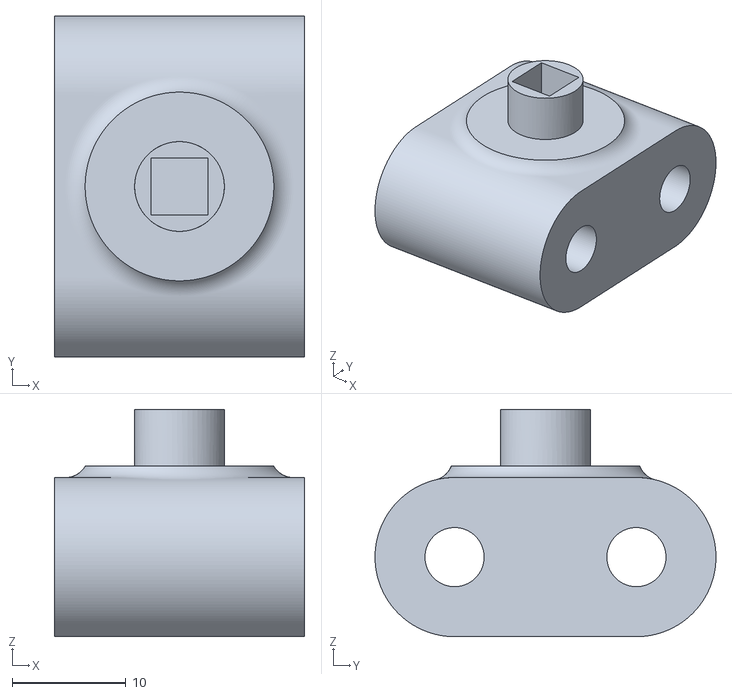
[picture p71: CAD file, 2026-03-30]
Joystick/STLs/Miramaksimus Base Updates/gimbal_core_pot_side.stl
22.0 x 30.0 x 20.0
