c0derMo/DIY-HOTAS/Joystick/STLs/Miramaksimus Base Updates/side_cover_blank.stl

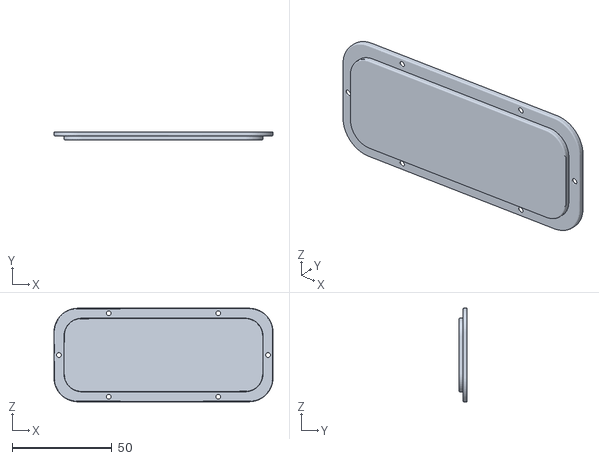
[picture p72: CAD file, 2026-03-30]
Joystick/STLs/Miramaksimus Base Updates/side_cover_blank.stl
110.0 x 4.00 x 47.0
