c0derMo/DIY-HOTAS/Joystick/STLs/Miramaksimus Base Updates/gimbal_core_bearing_carrier.stl

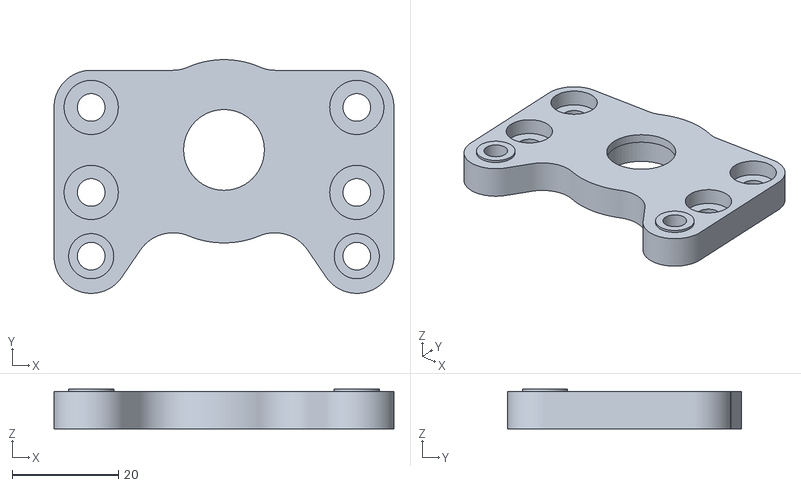
[picture p73: CAD file, 2026-03-30]
Joystick/STLs/Miramaksimus Base Updates/gimbal_core_bearing_carrier.stl
64.0 x 44.0 x 7.50
