c0derMo/DIY-HOTAS/Joystick/STLs/Miramaksimus Base Updates/front_cover_blank.stl

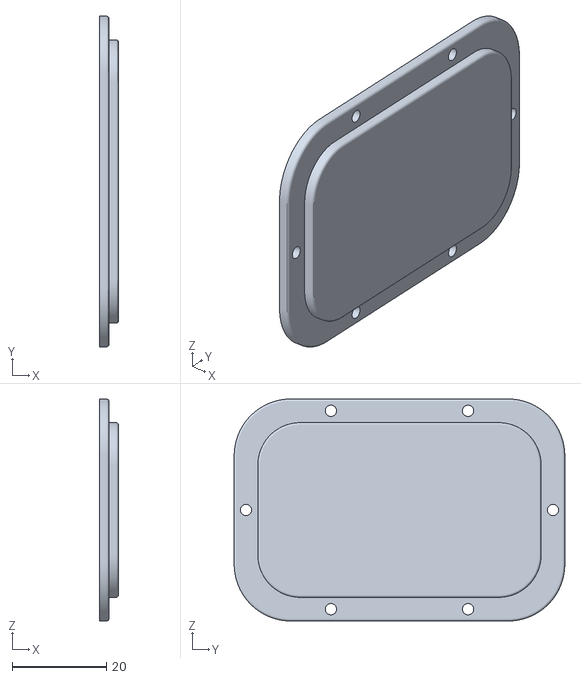
[picture p74: CAD file, 2026-03-30]
Joystick/STLs/Miramaksimus Base Updates/front_cover_blank.stl
4.00 x 70.0 x 47.0
